WDTY/mini-minitel-esp32-case/archive/development/v0.5-rear-bay-fixture/stl/minitel_guide_coupon_v0.5-test.stl

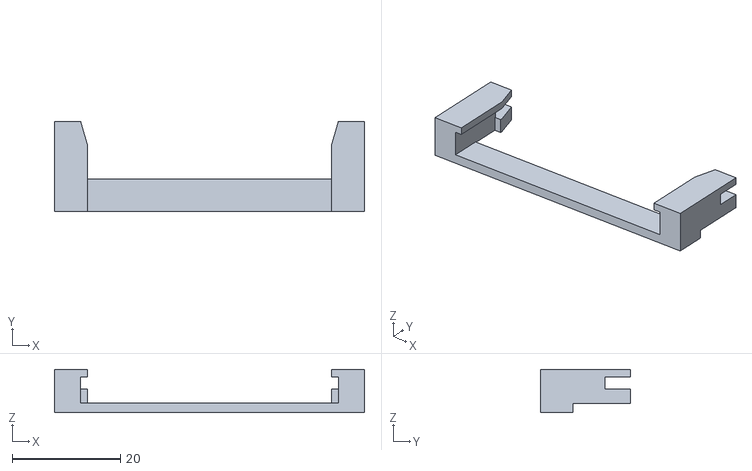
[picture p33: CAD file, 2026-09-19, an earlier design]
archive/development/v0.5-rear-bay-fixture/stl/minitel_guide_coupon_v0.5-test.stl
57.4 x 16.7 x 8.00
