WDTY/mini-minitel-esp32-case/archive/v0.1/minitel_front_v0.1.stl

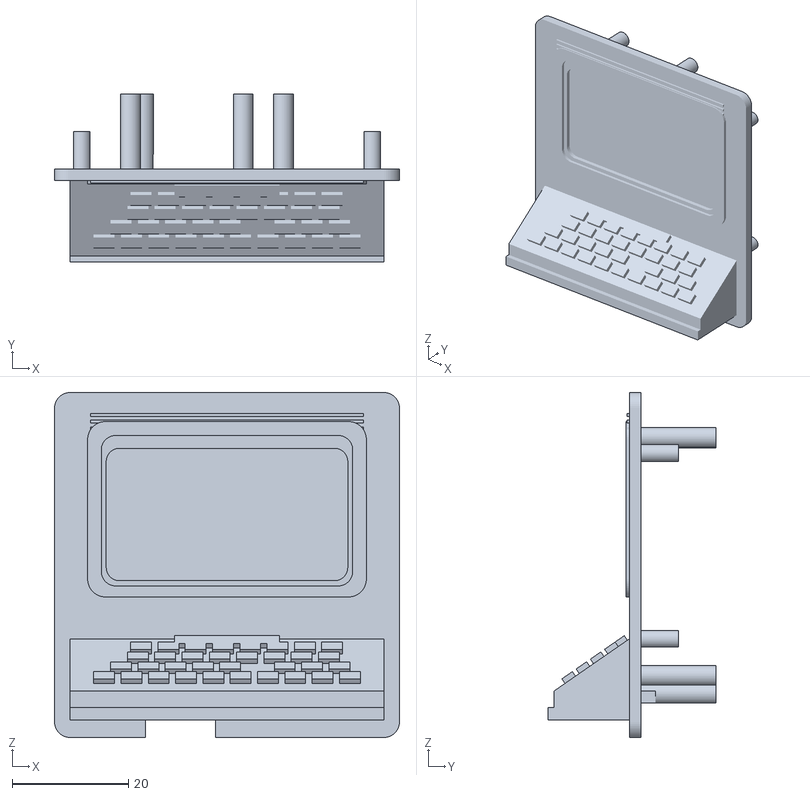
[picture p34: CAD file, 2026-09-17, an earlier design]
archive/v0.1/minitel_front_v0.1.stl
59.4 x 28.9 x 59.4
