WDTY/mini-minitel-esp32-case/src/render_reference.scad

// Render-only reference, not a printable assembly.
use <pcb_reference.scad>
pcb_reference();
